ahmsville/Magnetic_rotary_encoding/PICO DEV M3/3D Printing Files/RP2040 ENCODER - BUTTON BASE-1.STL

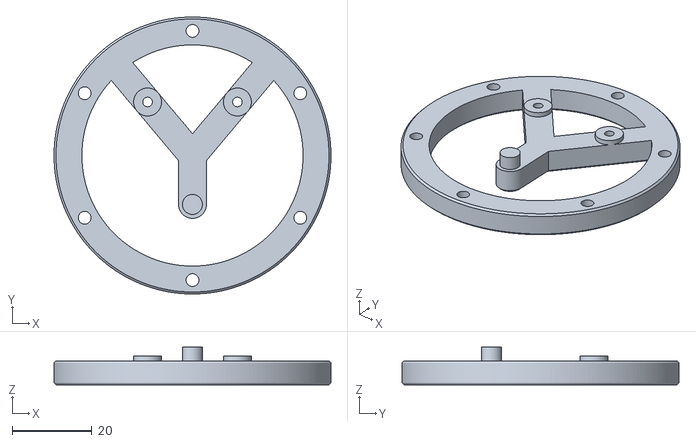
[picture p27: CAD file, 2023-01-05]
PICO DEV M3/3D Printing Files/RP2040 ENCODER - BUTTON BASE-1.STL
69.4 x 69.4 x 9.40
