ahmsville/Magnetic_rotary_encoding/CAD/Magnetic Rotary Encoder/DEFAULT SIZE/MAGNETIC ENCODER NORMAL - SLOT-1.STL

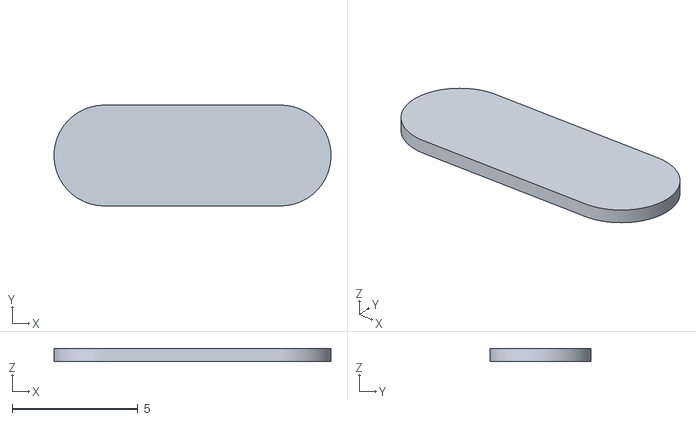
[picture p28: CAD file, 2023-01-05]
CAD/Magnetic Rotary Encoder/DEFAULT SIZE/MAGNETIC ENCODER NORMAL - SLOT-1.STL
11.0 x 4.00 x 0.5
