ahmsville/Magnetic_rotary_encoding/PICO DEV M3/3D Printing Files/RP2040 ENCODER - BOARD BUTTOM-1.STL

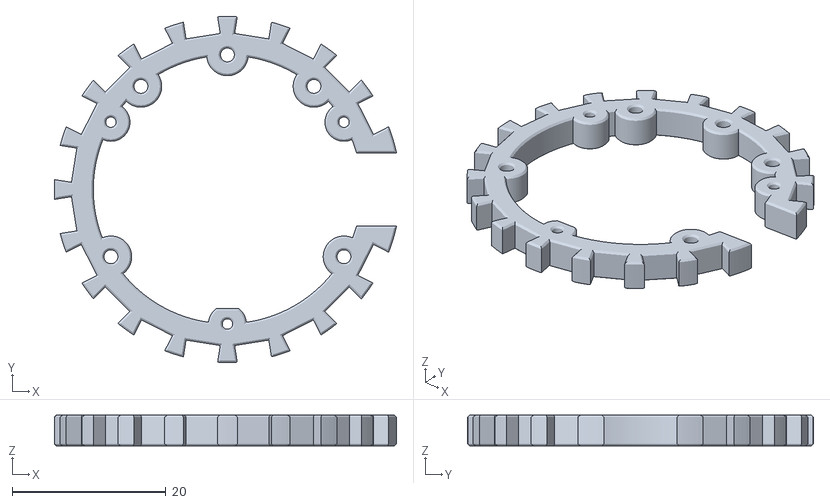
[picture p29: CAD file, 2023-01-05]
PICO DEV M3/3D Printing Files/RP2040 ENCODER - BOARD BUTTOM-1.STL
44.5 x 45.0 x 4.00
