ahmsville/Magnetic_rotary_encoding/CAD/Magnetic Rotary Encoder/MINI ENCODER/MINI ENCODER- - MOUNTING BASE-1.STL

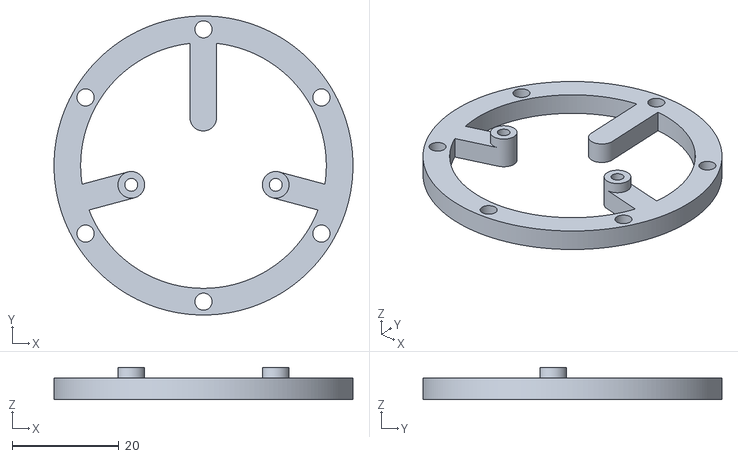
[picture p30: CAD file, 2023-02-22]
CAD/Magnetic Rotary Encoder/MINI ENCODER/MINI ENCODER- - MOUNTING BASE-1.STL
56.0 x 56.0 x 6.00
