ahmsville/Magnetic_rotary_encoding/PICO DEV M3/3D Printing Files/RP2040 ENCODER - SLOT-1.STL

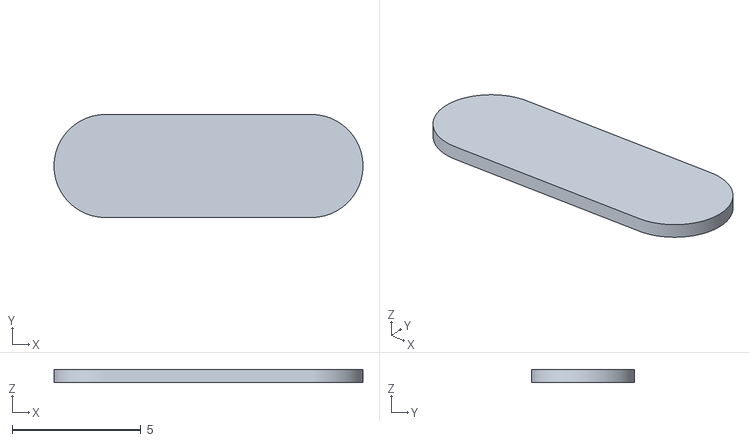
[picture p31: CAD file, 2023-01-05]
PICO DEV M3/3D Printing Files/RP2040 ENCODER - SLOT-1.STL
12.0 x 4.00 x 0.5
