ahmsville/Magnetic_rotary_encoding/Arduino/ADCRead/ADCRead.cpp

#include "ADCRead.h"

/*

Copyright (c) Ahmed Oyenuga (Ahmsville 2020).

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

*/







bool ADCRead::doneReading = true;


ADCRead::ADCRead() {
#ifdef adcres 
#if adcres == 10 
	//analogReadResolution(10);

#elif adcres == 12 
	//analogReadResolution(12);
#endif
#endif // adcres 
}


int ADCRead::Read(int pin) {
	if (ADCRead::doneReading) { 
		ADCRead::doneReading = false;
		analogvalue = analogRead(pin); //read adc
		ADCRead::doneReading = true;
	}
	else {
		analogvalue = 0;
	}
	
	return analogvalue;
}
